tmssngr/arduino-eeprommer/arduino/Eprommer595/data_ub8830_jute6k_modified_keyboard.h

#ifndef DATA_H
#define DATA_H
const static uint8_t DATA[] PROGMEM = {
	0x08, 0x00, 0x08, 0x03, 0x08, 0x06, 0x08, 0x09, 0x08, 0x0c, 0x08, 0x0f, 0x31, 0x00, 0x3c, 0x0f, // 0000
	0xff, 0x76, 0xe3, 0x04, 0x3c, 0xff, 0xeb, 0x05, 0x76, 0xe3, 0x04, 0xeb, 0x20, 0xe6, 0xf8, 0xb6, // 0010
	0xe6, 0xf7, 0x08, 0x4c, 0x08, 0x5c, 0x12, 0xc2, 0x64, 0x60, 0xe6, 0xd2, 0x64, 0xc2, 0x74, 0x60, // 0020
	0xe6, 0xd2, 0x64, 0xb2, 0x67, 0x31, 0xf0, 0xed, 0xe0, 0x00, 0x8d, 0x08, 0x12, 0xe6, 0xf8, 0x04, // 0030
	0xe6, 0xf1, 0xc0, 0x0c, 0xff, 0x1c, 0xff, 0xcf, 0x56, 0xe3, 0xdf, 0x46, 0xe3, 0x20, 0x10, 0xe1, // 0040
	0x10, 0xe0, 0x76, 0xe3, 0x04, 0x6b, 0x04, 0x7b, 0xf5, 0x8b, 0xed, 0xe6, 0xf8, 0x7f, 0x8b, 0xfe, // 0050
	0x46, 0x7f, 0x18, 0xe4, 0x7f, 0xf8, 0x56, 0x03, 0xdf, 0x76, 0x03, 0x04, 0x6b, 0xfb, 0x56, 0x7f, // 0060
	0xf7, 0x46, 0x03, 0x20, 0xe4, 0x7f, 0xf8, 0xff, 0xbf, 0x28, 0xe4, 0x38, 0xe5, 0xaf, 0x02, 0x35, // 0070
	0x12, 0x24, 0x4b, 0x16, 0xaf, 0x22, 0x35, 0x32, 0x24, 0x4b, 0x0f, 0xaf, 0x76, 0xe4, 0x80, 0x6b, // 0080
	0xe8, 0xb0, 0xe2, 0xb0, 0xe3, 0x8b, 0xee, 0x46, 0x0f, 0x80, 0x46, 0x0e, 0x80, 0xaf, 0x88, 0xe2, // 0090
	0xb2, 0x84, 0x9c, 0x02, 0x68, 0xe2, 0x78, 0xe3, 0xd6, 0x00, 0x8c, 0x48, 0xe6, 0x58, 0xe7, 0x9a, // 00a0
	0xf3, 0x68, 0xe2, 0x78, 0xe3, 0xb0, 0xe2, 0xb0, 0xe3, 0xaf, 0xd6, 0x00, 0x9e, 0xbc, 0x0f, 0xd0, // 00b0
	0xe6, 0xc0, 0xe7, 0xfb, 0x06, 0x02, 0x35, 0x12, 0x24, 0x4b, 0xcc, 0x10, 0xe5, 0x10, 0xe4, 0xcb, // 00c0
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
	0x20, 0x92, 0x20, 0x80, 0x60, 0x9a, 0xfa, 0xd6, 0x18, 0xd8, 0x8b, 0xaa, 0xaa, 0x1e, 0x9c, 0x20, // 1260
	0xec, 0xfc, 0xfc, 0x00, 0xac, 0x03, 0xbc, 0xc0, 0x92, 0x9e, 0xa0, 0x5e, 0x80, 0x5a, 0xeb, 0xf8, // 1270
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
};
const int DATA_LENGTH = 0x2000;
#endif
